tebl/BE6502-Build-a-65c02-computer/BE6502 Clock/gallery/2019-11-27 20.39.18.jpg

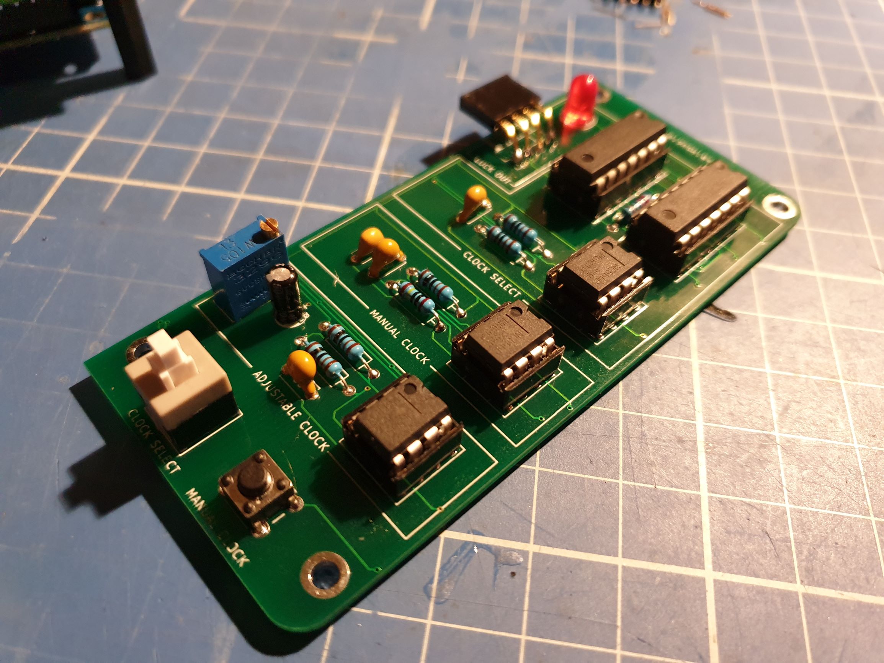
BE6502 Clock/gallery/2019-11-27 20.39.18.jpg
