tebl/BE6502-Build-a-65c02-computer/BE6502 SBC/gallery/2019-11-22 20.12.40.jpg

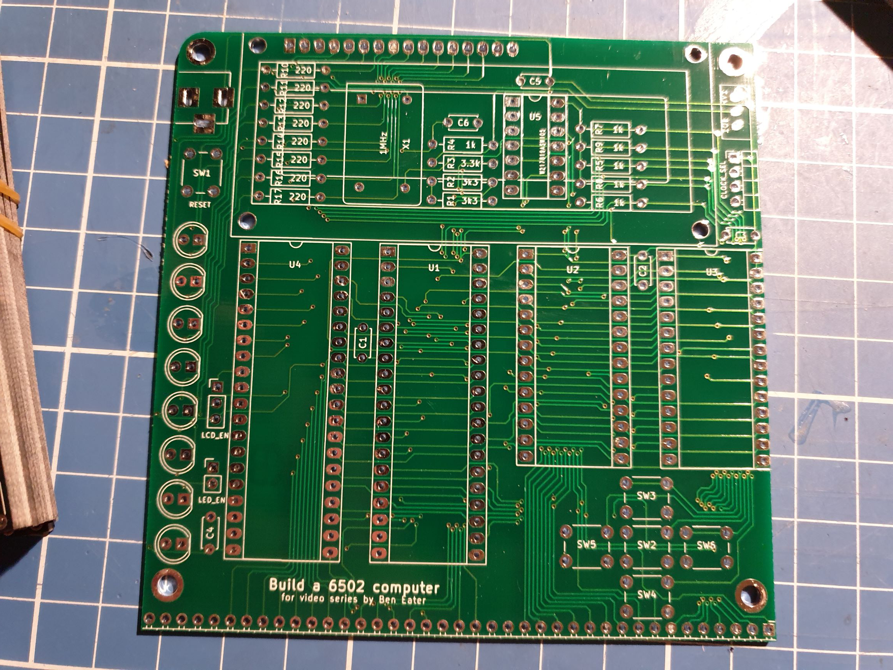
BE6502 SBC/gallery/2019-11-22 20.12.40.jpg
