tebl/BE6502-Build-a-65c02-computer/gallery/2020-02-22 20.33.05.jpg

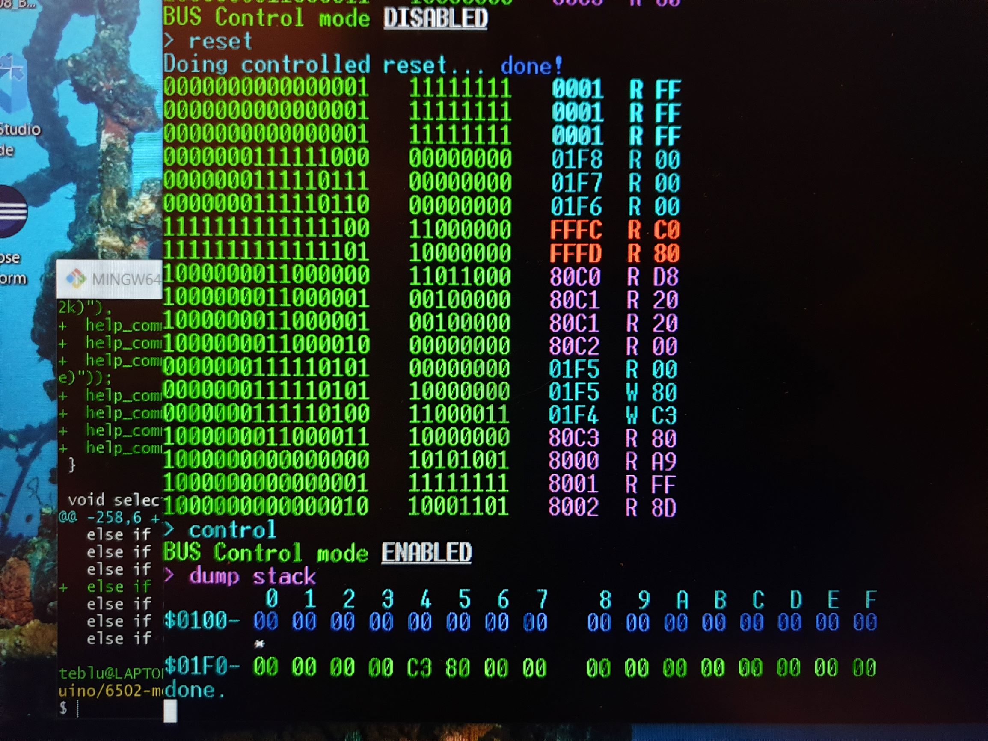
gallery/2020-02-22 20.33.05.jpg
