tebl/BE6502-Build-a-65c02-computer/gallery/BE6502 SBC.png

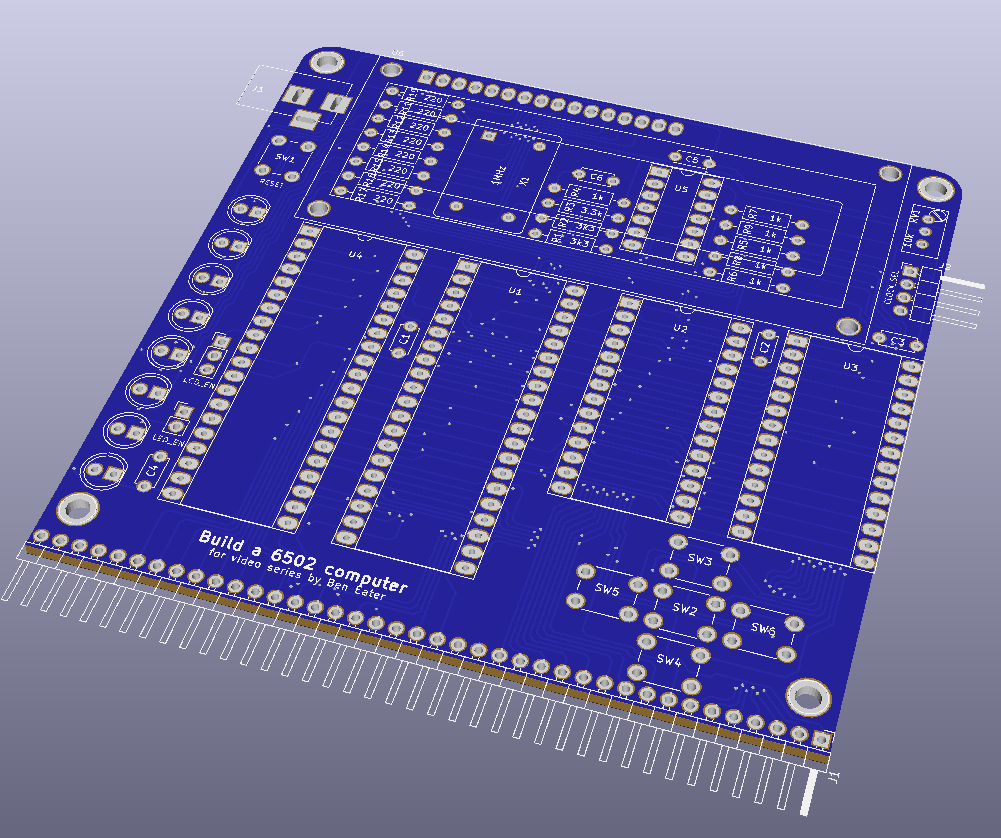
gallery/BE6502 SBC.png
