tebl/BE6502-Build-a-65c02-computer/gallery/Screenshot 2021-11-30 194604.png

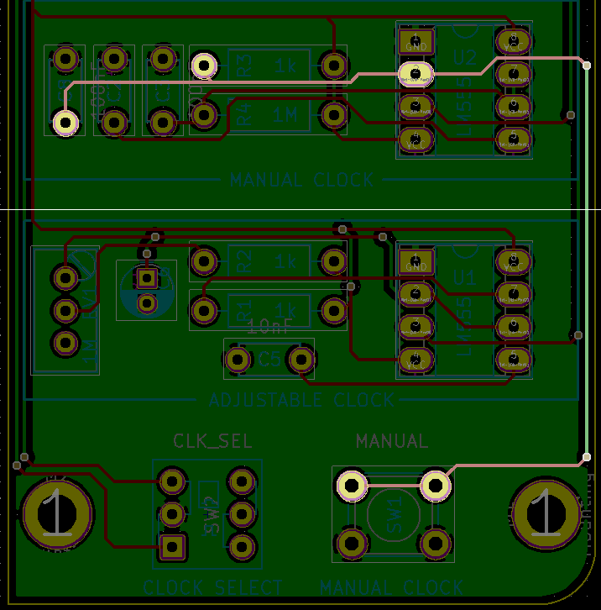
gallery/Screenshot 2021-11-30 194604.png
