tebl/BE6502-Build-a-65c02-computer/software/arduino/6502-monitor/6502-monitor/commands.h

#include "typedefs.h"

void commands_init();

void set_auto_clock();
void set_manual_clock();
void do_tick();
void do_reset();
void on_clock();
void print_help();
void print_version();
void print_welcome();
void set_monitor_off();
void set_monitor_on();

bool handle_command(String command, String name, void (*function)());
void select_command(String command);
void select_command(int user_switch, switch_functions_t* r);
void echo_command(String command);
void echo_unknown(String command);
