tebl/BE6502-Build-a-65c02-computer/software/arduino/6502-monitor/6502-monitor/debug.cpp

#include <Arduino.h>
#include "constants.h"
#include "ansi.h"

void debug(const char *string) {
  #ifdef DEBUG
  ansi_debug_ln(string);
  #endif
}

void debug(const __FlashStringHelper *string) {
  #ifdef DEBUG
  ansi_debug_ln(string);
  #endif
}
