tebl/BE6502-Build-a-65c02-computer/software/arduino/6502-monitor/6502-monitor/clock.h

void clock_initialize();
void do_reset();

void print_clock();
void set_external_clock();

void set_auto_clock();
void set_clock_1Hz();
void set_clock_2Hz();
void set_clock_4Hz();
void set_clock_16Hz();
void set_clock_32Hz();
void set_clock_128Hz();
void set_clock_256Hz();
void do_toggle_speed();

void set_manual_clock();
void do_manual_tick();

void int_attach();
void int_detach();
void set_monitor_on();
void set_monitor_off();
