tebl/BE6502-Build-a-65c02-computer/software/examples/001 - Blink/count.asm

* ---------------------------------------------------------
* Count up in binary, this has no delays built in so you'd
* need to use the clock module in order to see the changes.


        .CR     65C02
        .TF     count.hex,INT
        
        .OR     $8000
        .TA     $0000

ORB     .EQ     $6000   VIA Port B data
ORA     .EQ     $6001   VIA Port B data
DDRB    .EQ     $6002   VIA DDRB
DDRA    .EQ     $6003   VIA DDRA


START   LDA     #$FF
        STA     DDRB
        LDA     #00
LOOP    STA     ORB
        INC
        JMP     LOOP

* ---------------------------------------------------------
* STORE VECTORS AT END OF EPROM.
        .OR     $FFFA
        .TA     $7FFA
        .DA     START   NMI VECTOR
        .DA     START   RESET VECTOR
        .DA     START   IRQ VECTOR
