tebl/BE6502-Build-a-65c02-computer/gallery/2020-01-19 00.14.26.jpg

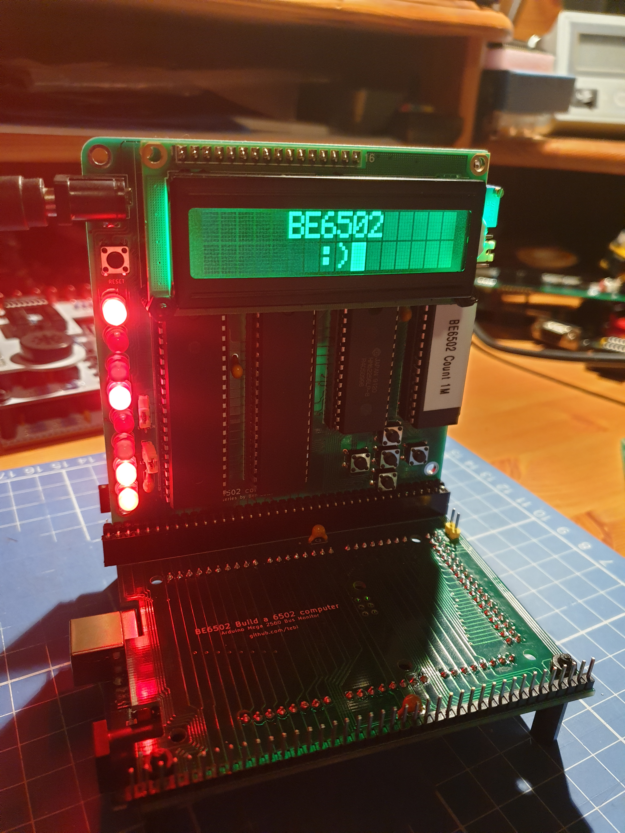
gallery/2020-01-19 00.14.26.jpg
